fredriknk/chatgpt_astra_test2/DOCUMENTATION/schematic_review/chatgpt_astra_test2-03 _ ESP32 AND USB.png

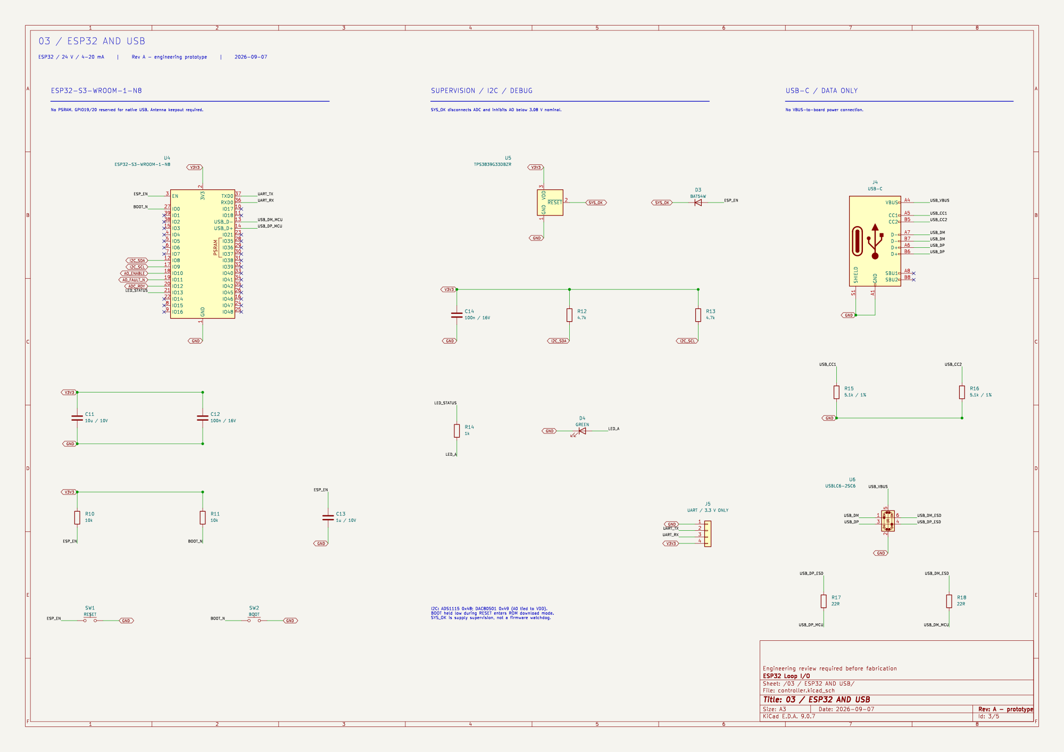
DOCUMENTATION/schematic_review/chatgpt_astra_test2-03 _ ESP32 AND USB.png
