fredriknk/chatgpt_astra_test2/DOCUMENTATION/schematic_review/png/chatgpt_astra_test2-02 _ POWER AND SENSOR SUPPLY.png

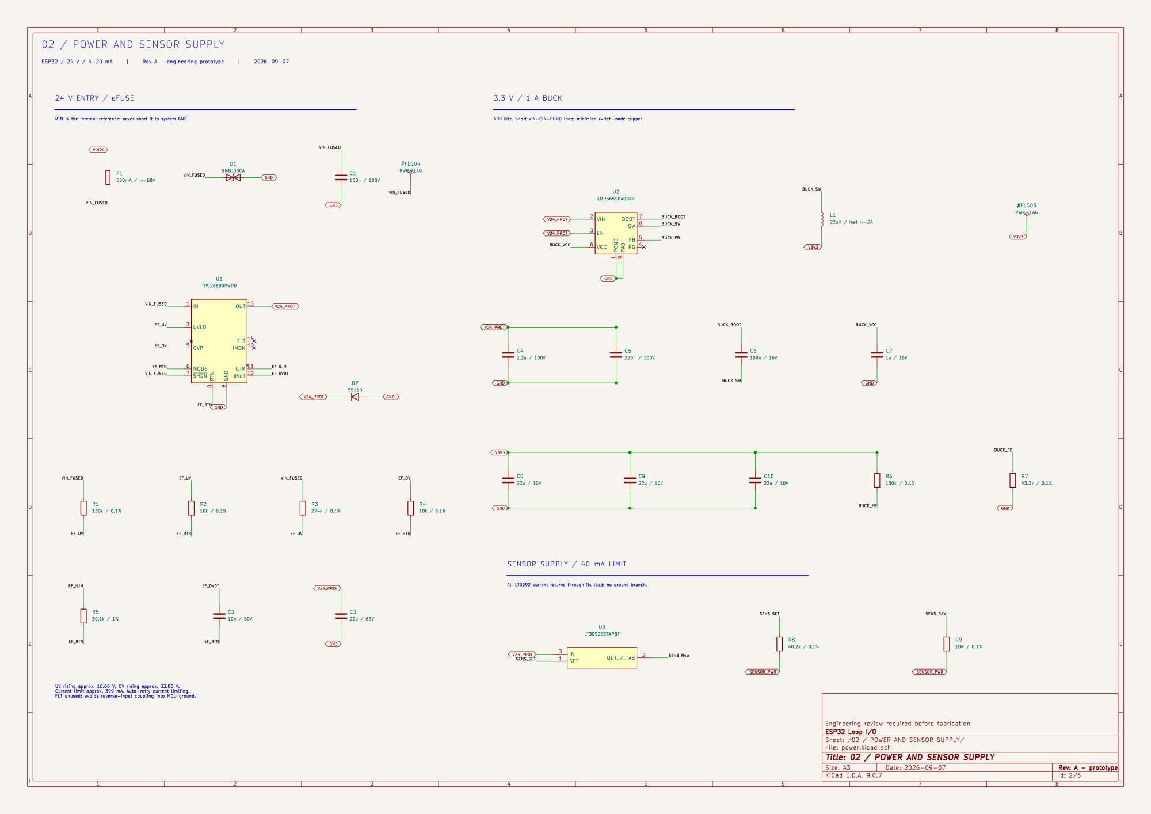
DOCUMENTATION/schematic_review/png/chatgpt_astra_test2-02 _ POWER AND SENSOR SUPPLY.png
