fredriknk/chatgpt_astra_test2/DOCUMENTATION/schematic_review/png/chatgpt_astra_test2-04 _ PROTECTED CURRENT INPUT.png

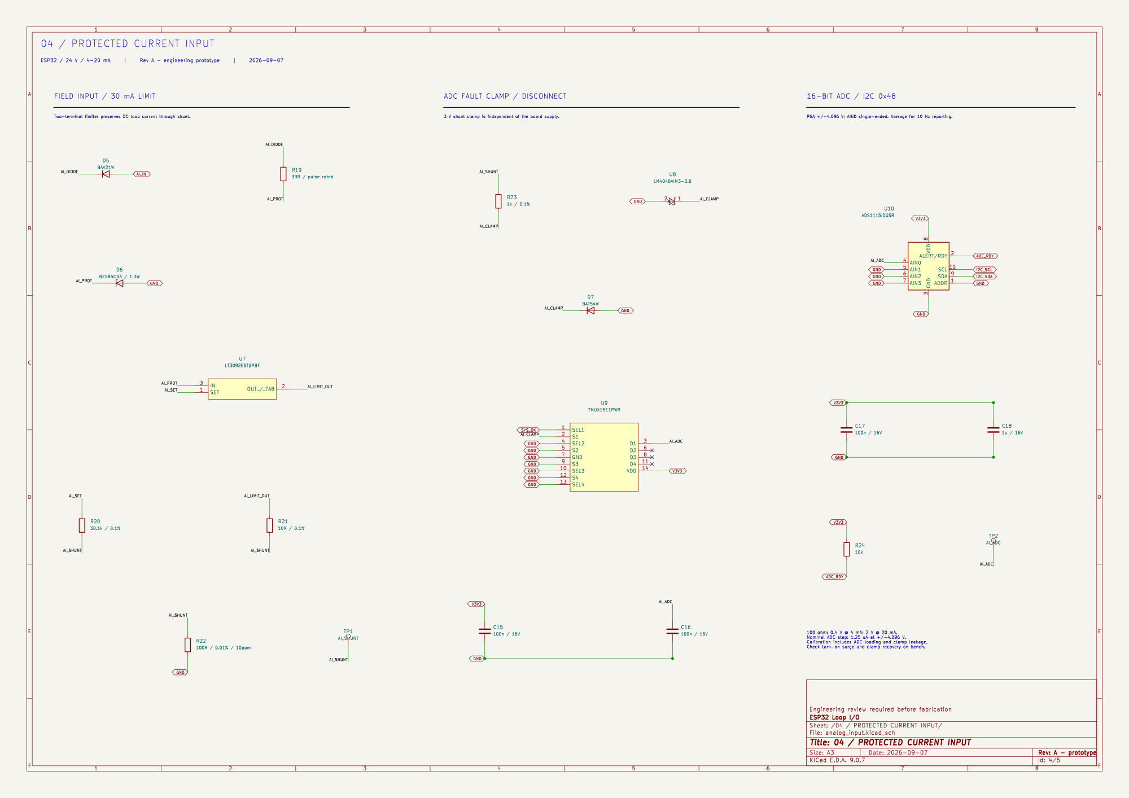
DOCUMENTATION/schematic_review/png/chatgpt_astra_test2-04 _ PROTECTED CURRENT INPUT.png
