fredriknk/chatgpt_astra_test2/DOCUMENTATION/schematic_review/png/chatgpt_astra_test2-05 _ PRECISION CURRENT OUTPUT.png

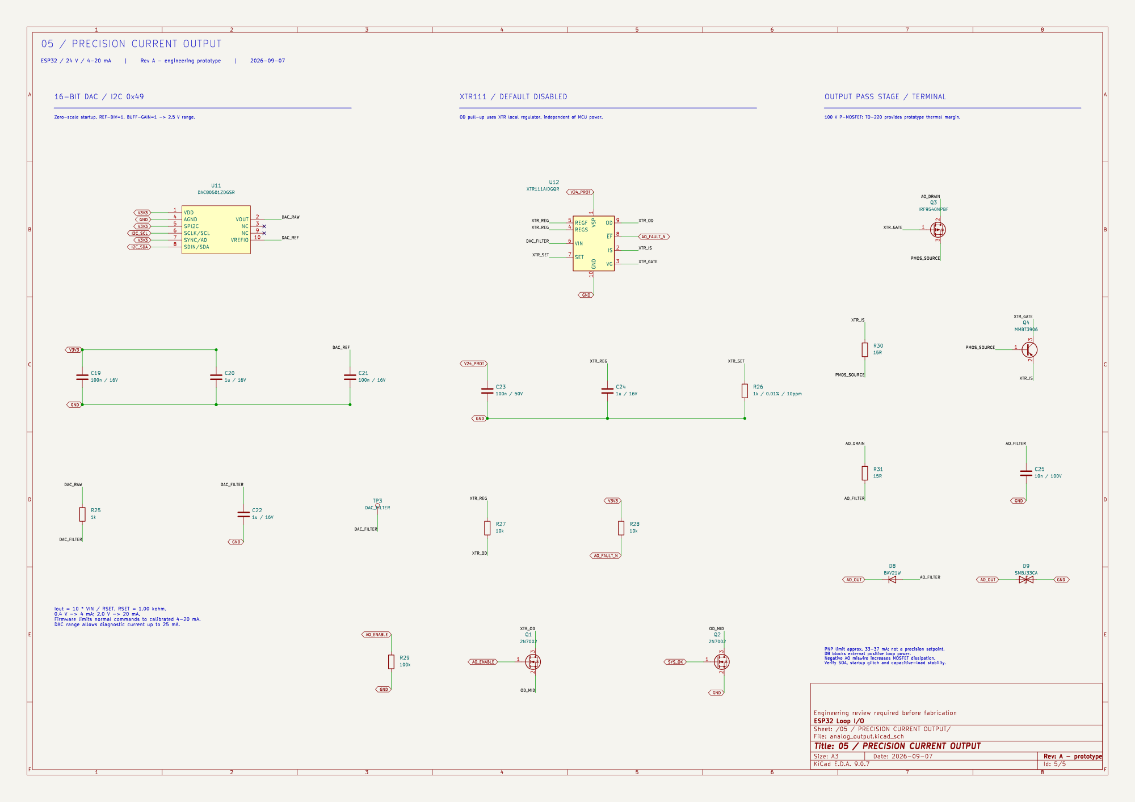
DOCUMENTATION/schematic_review/png/chatgpt_astra_test2-05 _ PRECISION CURRENT OUTPUT.png
