fredriknk/chatgpt_astra_test2/DOCUMENTATION/schematic_review/png/chatgpt_astra_test2.png

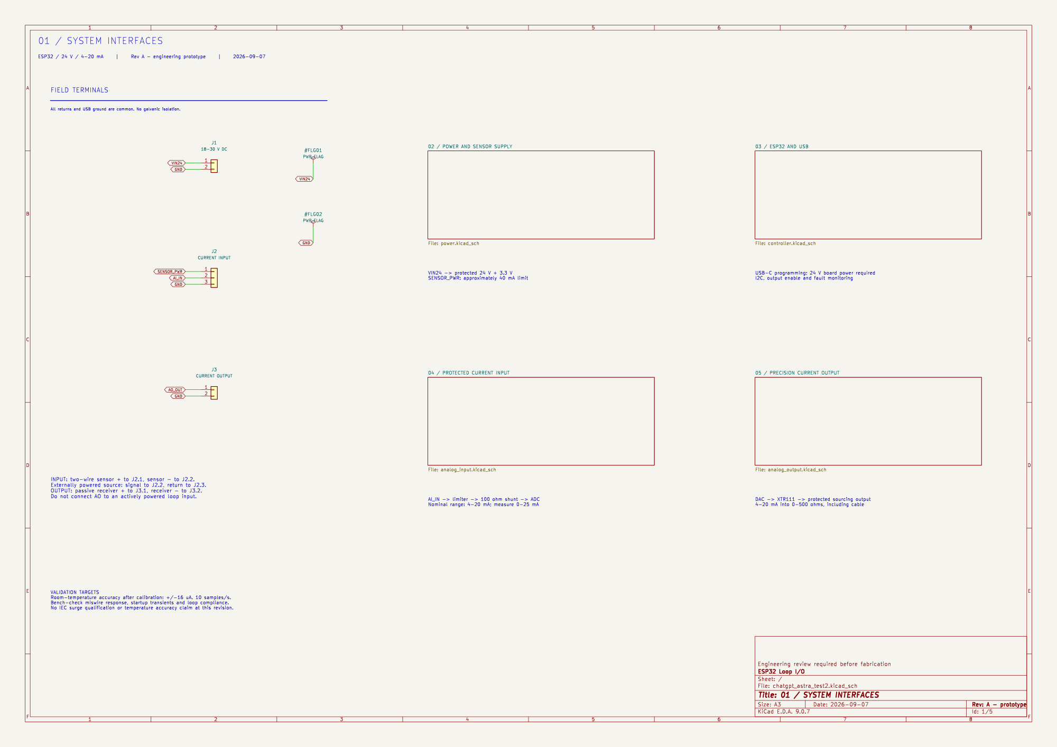
DOCUMENTATION/schematic_review/png/chatgpt_astra_test2.png
