fredriknk/chatgpt_astra_test2/PICTURES/chatgpt_astra_test2_bottom.png

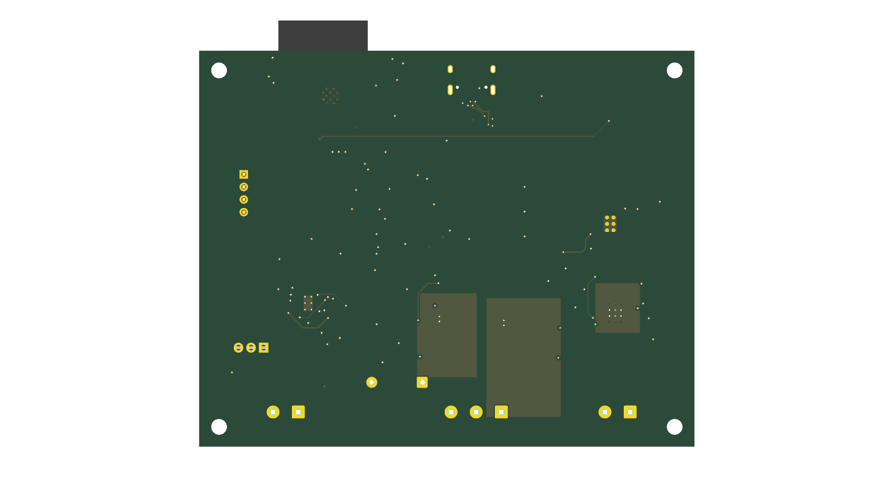
PICTURES/chatgpt_astra_test2_bottom.png
